Chrismettal/flipper-zero-backpacks/img/3D_Only.jpg

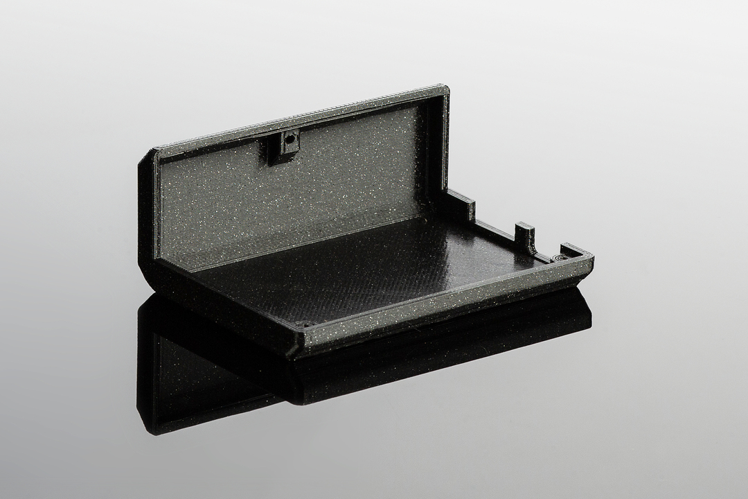
img/3D_Only.jpg
