Chrismettal/flipper-zero-backpacks/img/BackCaseWifi.png

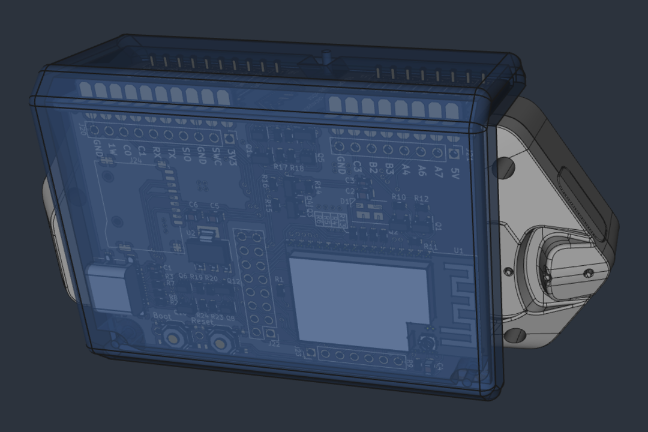
img/BackCaseWifi.png
