Chrismettal/flipper-zero-backpacks/img/NiceCaseBack.jpg

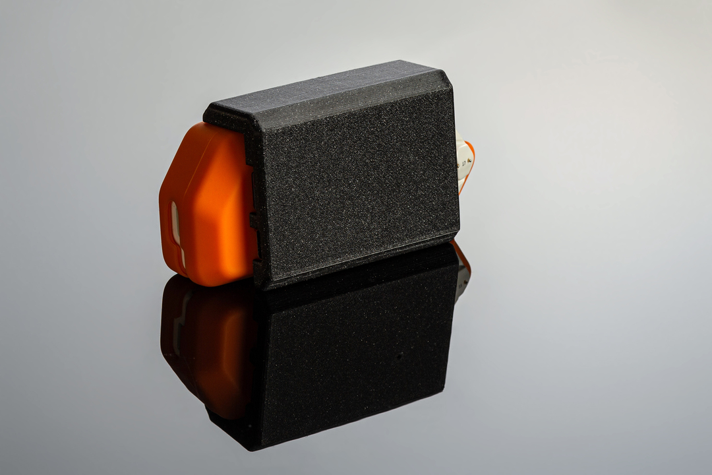
img/NiceCaseBack.jpg
