Chrismettal/flipper-zero-backpacks/img/NiceCaseFront.jpg

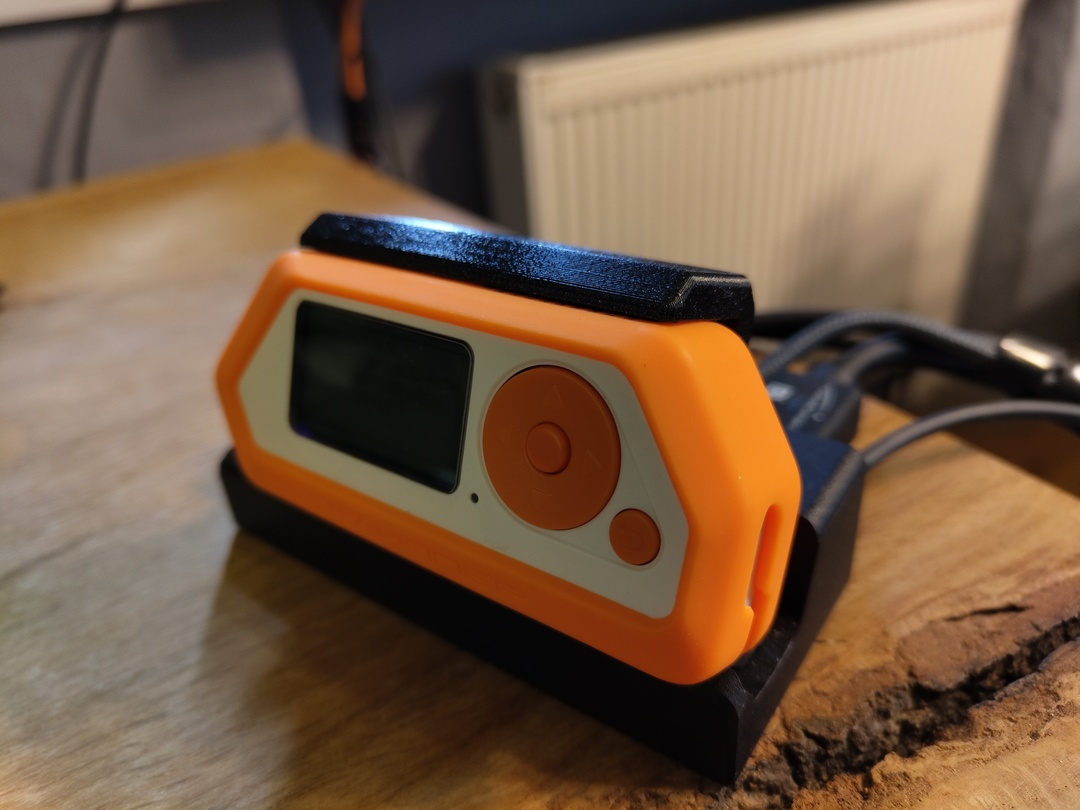
img/NiceCaseFront.jpg
