Chrismettal/flipper-zero-backpacks/img/NiceCaseTop.jpg

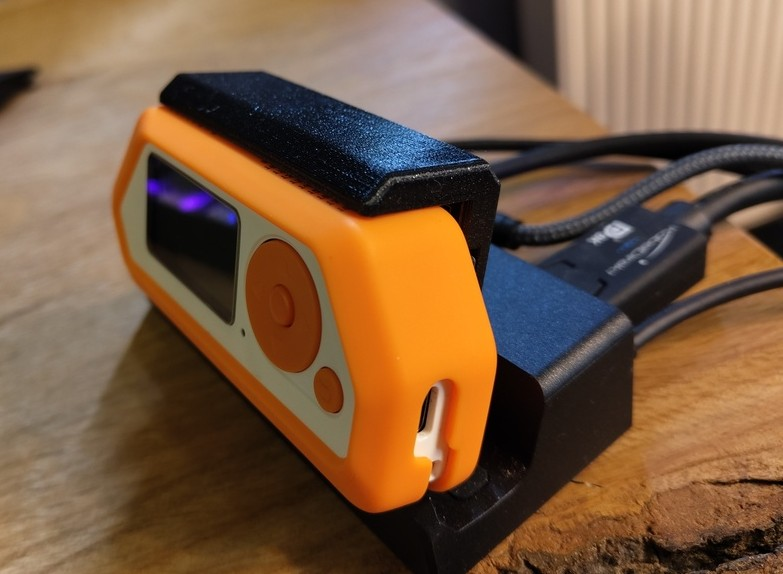
img/NiceCaseTop.jpg
