Chrismettal/flipper-zero-backpacks/img/NiceFront.jpg

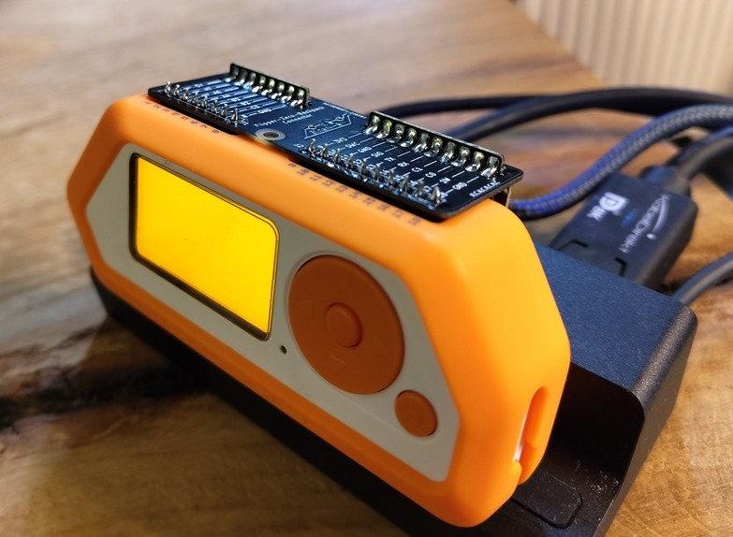
img/NiceFront.jpg
