Chrismettal/flipper-zero-backpacks/img/NiceTop.jpg

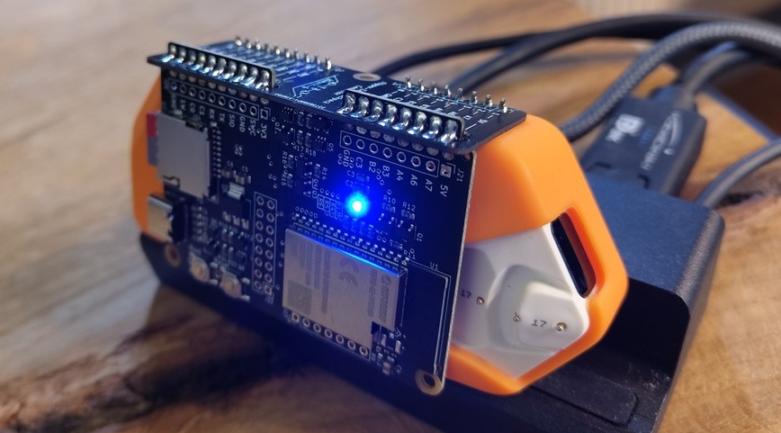
img/NiceTop.jpg
