Chrismettal/flipper-zero-backpacks/img/ProtoNiceBack.jpg

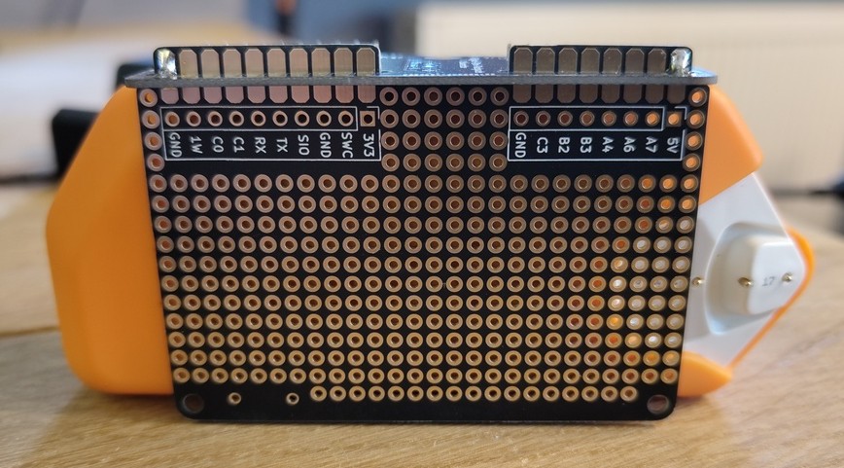
img/ProtoNiceBack.jpg
