Chrismettal/flipper-zero-backpacks/img/ProtoNiceFrontTop.jpg

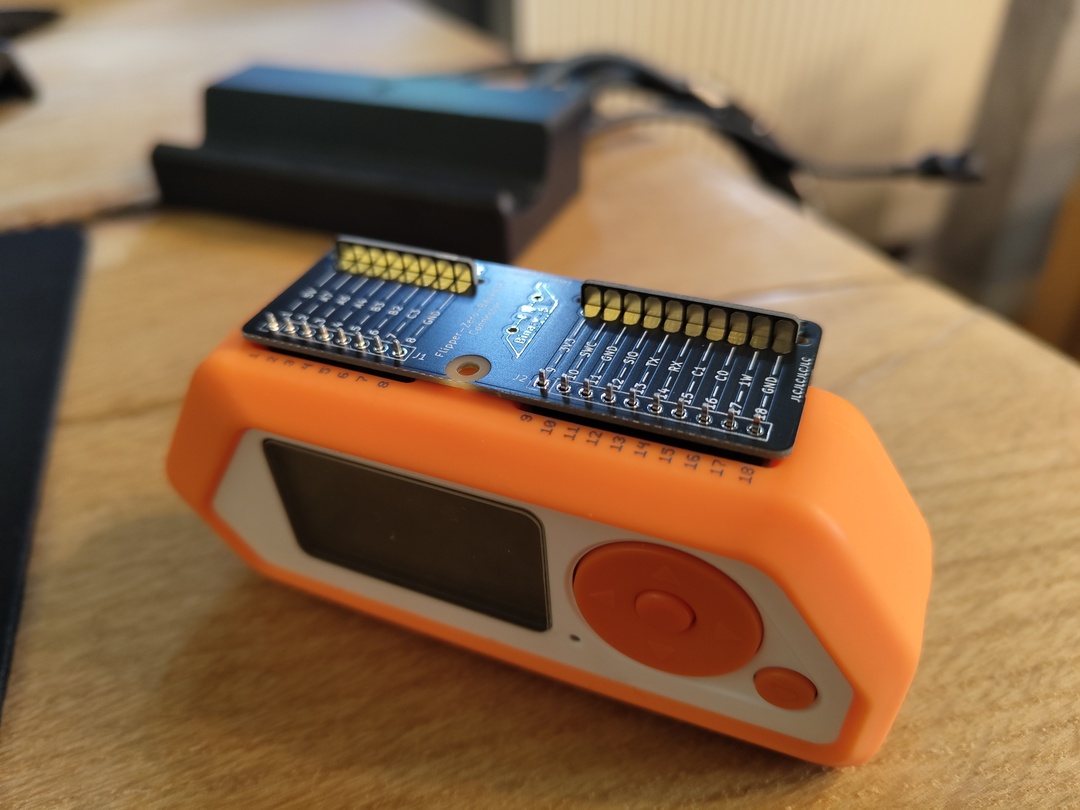
img/ProtoNiceFrontTop.jpg
