Chrismettal/flipper-zero-backpacks/img/Raspberry.jpg

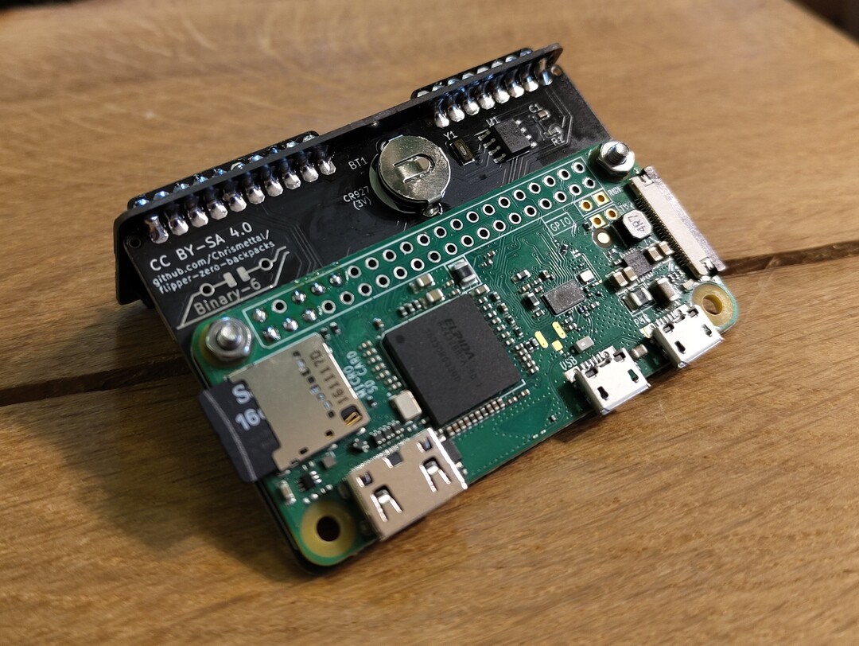
img/Raspberry.jpg
