Chrismettal/flipper-zero-backpacks/img/Supply.jpg

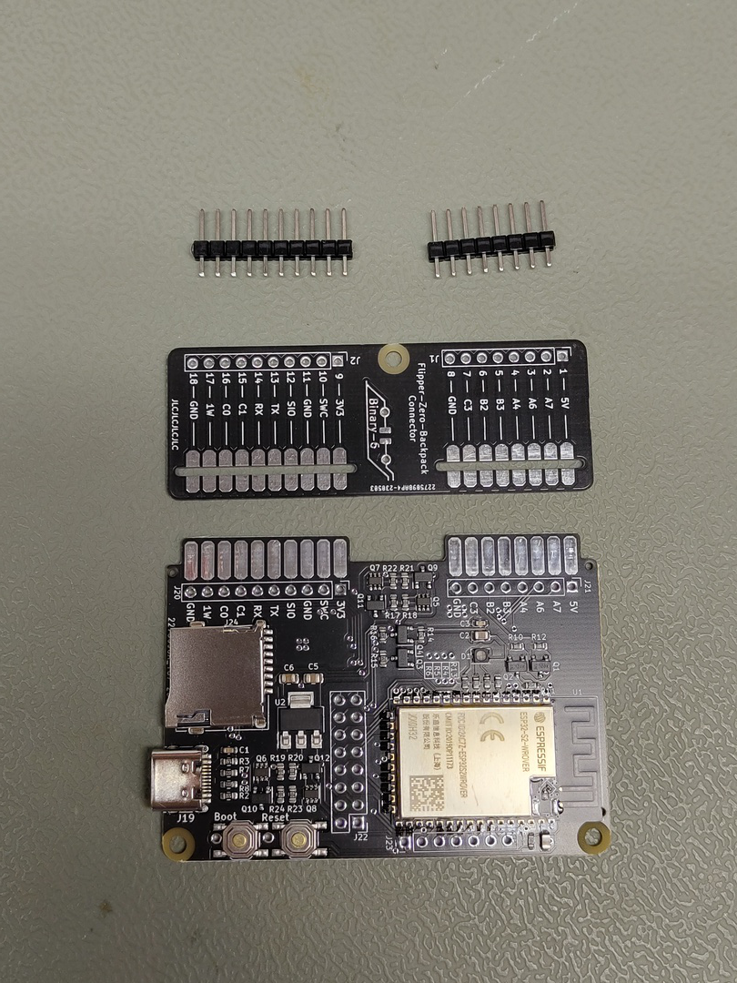
img/Supply.jpg
