Chrismettal/flipper-zero-backpacks/img/Wifi.png

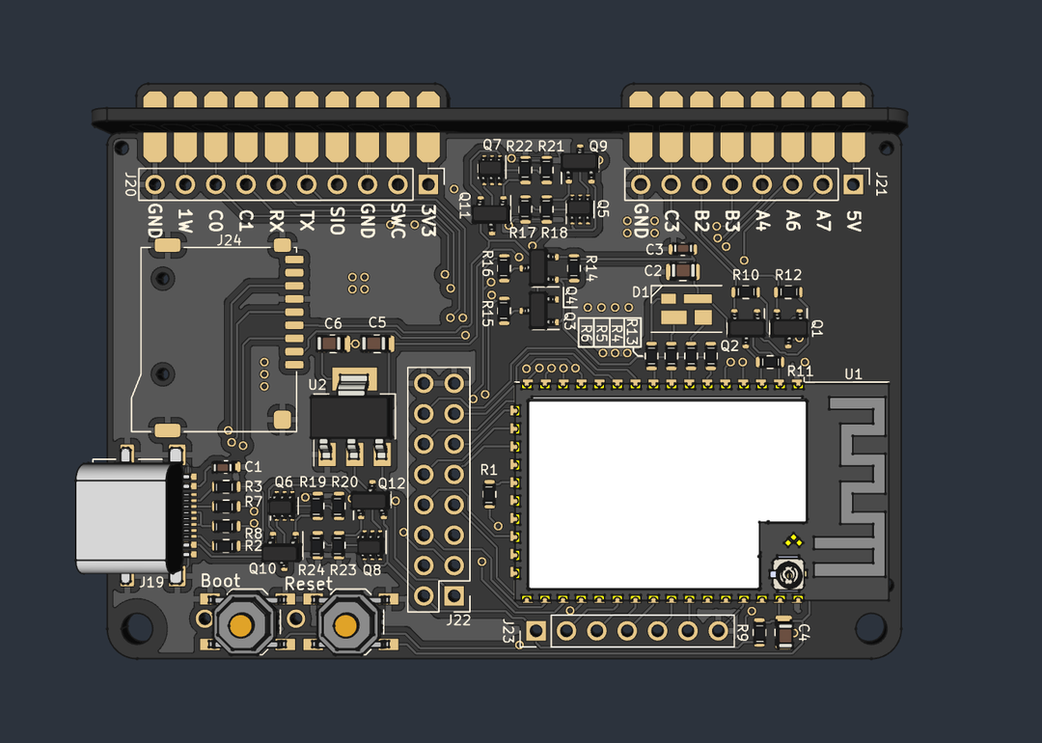
img/Wifi.png
